MateoCignetti/Hornito2023/Codigo/hornito-espA/main/adc.c

#include "adc.h"

// Defines
#define ADC1_DESIRED_BITWIDTH ADC_BITWIDTH_12   // Defines the desired bitwidth for ADC1
#define ADC2_DESIRED_BITWIDTH ADC_BITWIDTH_12   // Defines the desired bitwidth for ADC2
#define MULTISAMPLE_SIZE 10                     // Defines the number of ADC readings to be taken in the multisampling function
#define MULTISAMPLE_DELAY_MS 5                  // Defines the delay between each ADC reading in the multisampling function

#define ADC_DEBUGGING_TASK 0                    // Defines and creates a task that reads all configured channels every 5 seconds.
                                                // Note: This task is only used for debugging and should not be used in production
#define ADC_DEBUGGING_TASK_DELAY_MS 1000        // Defines the period of the ADC debugging task mentioned above

// Global variables
static const int ADC1_CHANNELS[] = {ADC_CHANNEL_0, ADC_CHANNEL_3, ADC_CHANNEL_6};   // Defines the channels to be configured on ADC1
static const int ADC2_CHANNELS[] = {};                                              // Defines the channels to be configured on ADC2
static const int ADC1_CHANNEL_COUNT = sizeof(ADC1_CHANNELS) / sizeof(int);          // Defines the number of channels to be configured on ADC1
static const int ADC2_CHANNEL_COUNT = sizeof(ADC2_CHANNELS) / sizeof(int);          // Defines the number of channels to be configured on ADC2
//

// ESP-LOG Tags
const static char* TAG_ADC = "ADC";
//

// Handles
static adc_oneshot_unit_handle_t adc1_handle;
static adc_cali_handle_t adc1_cali_handle;
static adc_oneshot_unit_handle_t adc2_handle;
static adc_cali_handle_t adc2_cali_handle;
#if ADC_DEBUGGING_TASK
static TaskHandle_t xTaskAdcDebug_handle;
#endif
//

// Private function prototypes
static void adc1_init();
static void adc2_init();
static void adc1_create_oneshot_unit();
static void adc1_calibration();
static void adc1_configure_channels();
static void adc2_create_oneshot_unit();
static void adc2_calibration();
static void adc2_configure_channels();
#if ADC_DEBUGGING_TASK
static void vTaskReadAllChannels();
#endif
//

// Functions

// Initializes both ADC units, should be called from main.c
void adc_init(){
    adc1_init();
    adc2_init();
}


// Creates the onesht unit, calibrates and configures the channels for ADC1
void adc1_init(){
    if(ADC1_CHANNEL_COUNT > 0){
        adc1_create_oneshot_unit();
        adc1_calibration();
        adc1_configure_channels();

        ESP_LOGI(TAG_ADC, "ADC1 Initialized");
    } else{
        ESP_LOGI(TAG_ADC, "ADC1 Not initialized, no channels configured");
    }
}


// Creates the oneshot unit, calibrates and configures the channels for ADC2
void adc2_init(){
    if(ADC2_CHANNEL_COUNT > 0){
        adc2_create_oneshot_unit();
        adc2_calibration();
        adc2_configure_channels();

        ESP_LOGI(TAG_ADC, "ADC2 Initialized");
    } else{
        ESP_LOGI(TAG_ADC, "ADC2 Not initialized, no channels configured");
    }
}

// Creates the oneshot unit for ADC1
static void adc1_create_oneshot_unit(){
    adc_oneshot_unit_init_cfg_t adc1_init_config = {
        .unit_id = ADC_UNIT_1,
    };

    ESP_ERROR_CHECK(adc_oneshot_new_unit(&adc1_init_config, &adc1_handle));
    ESP_LOGI(TAG_ADC, "ADC1 Oneshot created");
}

// Creates the oneshot unit for ADC2
static void adc2_create_oneshot_unit(){
    adc_oneshot_unit_init_cfg_t adc2_init_config = {
        .unit_id = ADC_UNIT_2,
    };

    ESP_ERROR_CHECK(adc_oneshot_new_unit(&adc2_init_config, &adc2_handle));
    ESP_LOGI(TAG_ADC, "ADC2 Oneshot created");
}

// Calibrates ADC1
static void adc1_calibration(){
    adc_cali_line_fitting_config_t adc1_cali_config = {
            .unit_id = ADC_UNIT_1,
            .atten = ADC_ATTEN_DB_11,
            .bitwidth = ADC1_DESIRED_BITWIDTH
    };

    ESP_ERROR_CHECK(adc_cali_create_scheme_line_fitting(&adc1_cali_config, &adc1_cali_handle));
    ESP_LOGI(TAG_ADC, "ADC1 Calibration completed");
}

// Calibrates ADC2
static void adc2_calibration(){
    adc_cali_line_fitting_config_t adc2_cali_config = {
            .unit_id = ADC_UNIT_2,
            .atten = ADC_ATTEN_DB_11,
            .bitwidth = ADC2_DESIRED_BITWIDTH
    };

    ESP_ERROR_CHECK(adc_cali_create_scheme_line_fitting(&adc2_cali_config, &adc2_cali_handle));
    ESP_LOGI(TAG_ADC, "ADC2 Calibration completed");
}

// Configures the defined channels for ADC1
static void adc1_configure_channels(){
    adc_oneshot_chan_cfg_t adc1_channel_configs[ADC1_CHANNEL_COUNT];
    for(int i = 0; i < ADC1_CHANNEL_COUNT; i++){
        adc1_channel_configs[i].atten = ADC_ATTEN_DB_11;
        adc1_channel_configs[i].bitwidth = ADC1_DESIRED_BITWIDTH;

        ESP_ERROR_CHECK(adc_oneshot_config_channel(adc1_handle, ADC1_CHANNELS[i], &adc1_channel_configs[i]));
        ESP_LOGI(TAG_ADC, "ADC1 Channel %d configured", ADC1_CHANNELS[i]);
    }
}

// Configures the defined channels for ADC2
static void adc2_configure_channels(){
    adc_oneshot_chan_cfg_t adc2_channel_configs[ADC2_CHANNEL_COUNT];
    for(int i = 0; i < ADC2_CHANNEL_COUNT; i++){
        adc2_channel_configs[i].atten = ADC_ATTEN_DB_11;
        adc2_channel_configs[i].bitwidth = ADC2_DESIRED_BITWIDTH;

        ESP_ERROR_CHECK(adc_oneshot_config_channel(adc2_handle, ADC2_CHANNELS[i], &adc2_channel_configs[i]));
        ESP_LOGI(TAG_ADC, "ADC2 Channel %d configured", ADC2_CHANNELS[i]);
    }
}

// Returns the voltage in mV from the ADC
int get_adc_voltage_mv(adc_unit_t ADC_UNIT, adc_channel_t ADC_CHANNEL){
    adc_oneshot_unit_handle_t adc_handle = NULL;
    adc_cali_handle_t adc_cali_handle = NULL;
    if(ADC_UNIT == ADC_UNIT_1){
        adc_handle = adc1_handle;
        adc_cali_handle = adc1_cali_handle;
    } else if(ADC_UNIT == ADC_UNIT_2){
        adc_handle = adc2_handle;
        adc_cali_handle = adc2_cali_handle;
    } else{
        ESP_LOGE(TAG_ADC, "Invalid ADC unit or channel");
        return 0;
    }

    int adc_voltage_mv = 0;
    adc_oneshot_get_calibrated_result(adc_handle, adc_cali_handle, ADC_CHANNEL, &adc_voltage_mv);
    
    return adc_voltage_mv;
}

// Returns the voltage in mV from the ADC with multisampling
int get_adc_voltage_mv_multisampling(adc_unit_t ADC_UNIT, adc_channel_t ADC_CHANNEL){
    adc_oneshot_unit_handle_t adc_handle = NULL;
    adc_cali_handle_t adc_cali_handle = NULL;
    if(ADC_UNIT == ADC_UNIT_1){
        adc_handle = adc1_handle;
        adc_cali_handle = adc1_cali_handle;
    } else if(ADC_UNIT == ADC_UNIT_2){
        adc_handle = adc2_handle;
        adc_cali_handle = adc2_cali_handle;
    } else{
        ESP_LOGE(TAG_ADC, "Invalid ADC unit or channel");
        return 0;
    }

    int adc_raw = 0;            //Defined as an int because VSCODE doesn't like uint16_t
    int adc_raw_sum = 0;        //Defined as an int because VSCODE doesn't like uint32_t
    int adc_voltage_mv = 0;     //Defined as an int because VSCODE doesn't like uint16_t
    
    for(int i = 0; i < MULTISAMPLE_SIZE; i++){
        adc_oneshot_get_calibrated_result(adc_handle, adc_cali_handle, ADC_CHANNEL, &adc_raw);
        adc_raw_sum += adc_raw;
        vTaskDelay(pdMS_TO_TICKS(MULTISAMPLE_DELAY_MS));
    }

    adc_voltage_mv = adc_raw_sum / MULTISAMPLE_SIZE;
    
    return adc_voltage_mv;      //Defined as an int because VSCODE doesn't like uint16_t
}

// Creates the ADC-related tasks
void create_adc_tasks(){
    #if ADC_DEBUGGING_TASK
    xTaskCreatePinnedToCore(vTaskReadAllChannels,
                            "ADC1 C0 read task",
                            configMINIMAL_STACK_SIZE * 10,
                            NULL,
                            tskIDLE_PRIORITY + 1,
                            &xTaskAdcDebug_handle,
                            0);
    #endif
}
//

// FreeRTOS Tasks
#if ADC_DEBUGGING_TASK
// Task that reads all configured channels every 5 seconds. Note: This task is only used for debugging and should not be used in production
static void vTaskReadAllChannels(){ 
    TickType_t xLastWakeTime = xTaskGetTickCount();
    while(true){
        for(int i = 0; i < ADC1_CHANNEL_COUNT; i++){
            int adc_voltage = 0;
            adc_oneshot_get_calibrated_result(adc1_handle, adc1_cali_handle, ADC1_CHANNELS[i], &adc_voltage);
            ESP_LOGI(TAG_ADC, "ADC1-C%d: %d mV", ADC1_CHANNELS[i], adc_voltage);
        }

        for(int i = 0; i < ADC2_CHANNEL_COUNT; i++){
            int adc_voltage = 0;
            adc_oneshot_get_calibrated_result(adc2_handle, adc2_cali_handle, ADC2_CHANNELS[i], &adc_voltage);
            ESP_LOGI(TAG_ADC, "ADC2-C%d: %d mV", ADC2_CHANNELS[i], adc_voltage);
        }

        vTaskDelayUntil(&xLastWakeTime, pdMS_TO_TICKS(ADC_DEBUGGING_TASK_DELAY_MS));
    }
}
#endif
//
