MateoCignetti/Hornito2023/TestVarios/simple-mav-filter-test/main/main.c

/*-------------- Includes --------------*/
#include <stdio.h>
#include <stdbool.h>
/*-------------- Defines ---------------*/
#define BUFFER_SIZE 10
#define MAV_SIZE BUFFER_SIZE/2

static uint16_t adcBuffer[BUFFER_SIZE]={1, 2, 1, 3, 2, 2, 1, 3, 4, 1}; // 00001 00012 00121 01213 12132 21322 13221
static uint16_t resultado[BUFFER_SIZE]={0};
static uint16_t mavBuffer[MAV_SIZE]={0};

/*------------- Function prototypes -----*/
void mav_filter(void);
void shift_mav_filter(void);

void app_main(void) {
    mav_filter();
}

/*---------------- Functions -----------------*/
void mav_filter(void){
    float sumMAV;
    float suma=0;
    for (int k = 0; k < BUFFER_SIZE; k++) {
        mavBuffer[0] = adcBuffer[k];
        sumMAV = 0;
        for(int j=0; j < MAV_SIZE; j++){
            sumMAV += mavBuffer[j];
        }
        shift_mav_filter();
        suma=sumMAV/(MAV_SIZE);
    }
}

void shift_mav_filter(void){
    for (int i = (MAV_SIZE-1); i > 0; i--) {
        mavBuffer[i] = mavBuffer[i-1];
    }    
}
