MateoCignetti/Hornito2023/TestVarios/adc-plot/include/adc.h

#ifndef ADC_H
#define ADC_H

#include "freertos/FreeRTOS.h"
#include "freertos/task.h"
#include "esp_adc/adc_cali.h"
#include "esp_adc/adc_cali_scheme.h"
#include "esp_adc/adc_oneshot.h"
#include "esp_log.h"

void adc1_init();
void create_adc_read_task();

#endif
